khinds10/XBox360Arcade/Construction/21.jpg

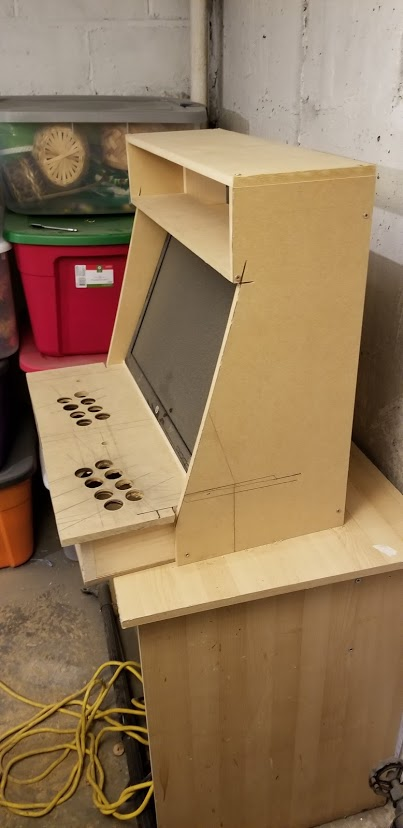
Construction/21.jpg
