khinds10/XBox360Arcade/Construction/24.jpg

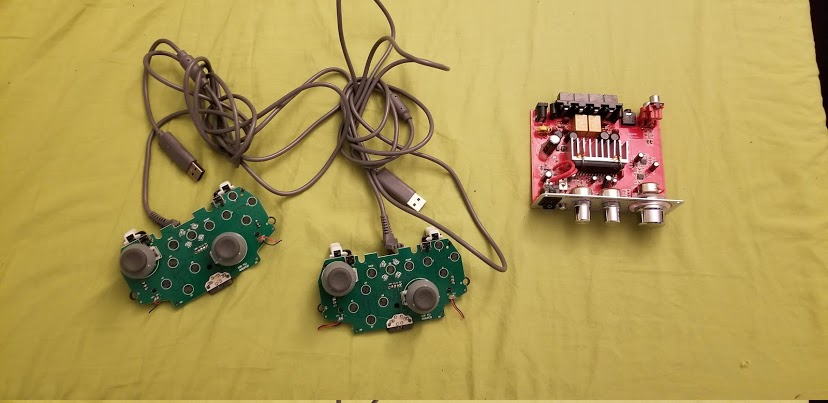
Construction/24.jpg
