khinds10/XBox360Arcade/Construction/25.jpg

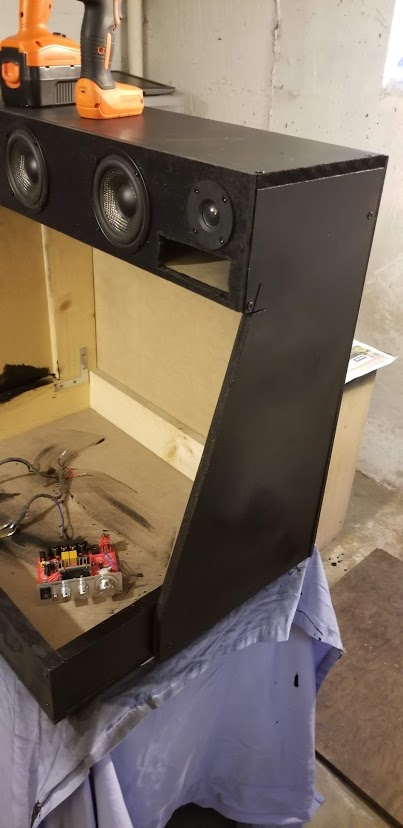
Construction/25.jpg
