khinds10/XBox360Arcade/Construction/29.jpg

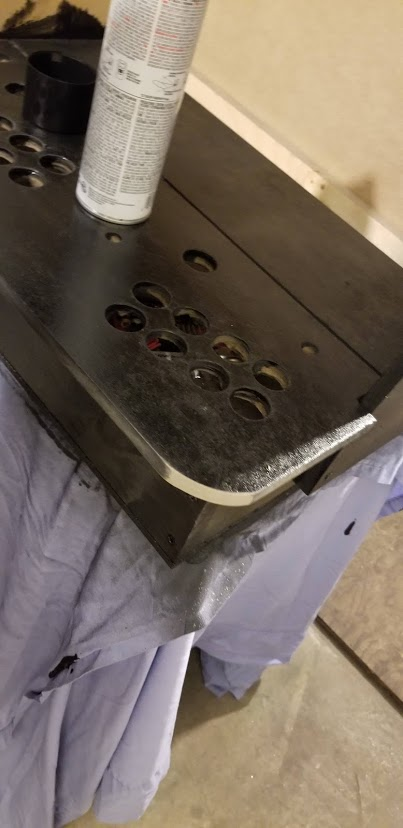
Construction/29.jpg
