khinds10/XBox360Arcade/Construction/35.jpg

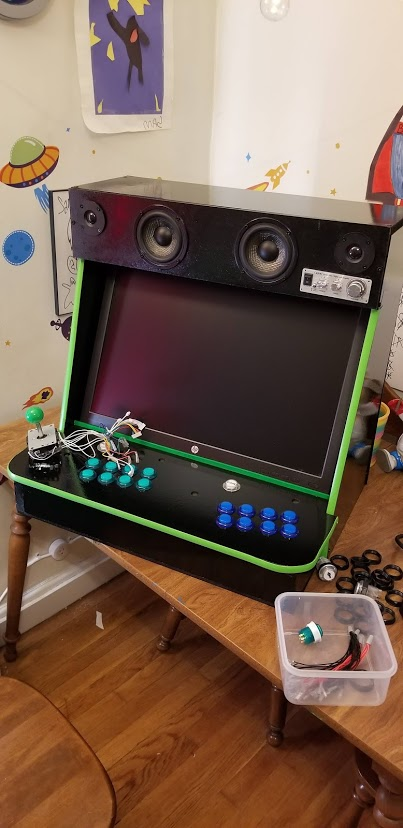
Construction/35.jpg
