khinds10/XBox360Arcade/Construction/36.jpg

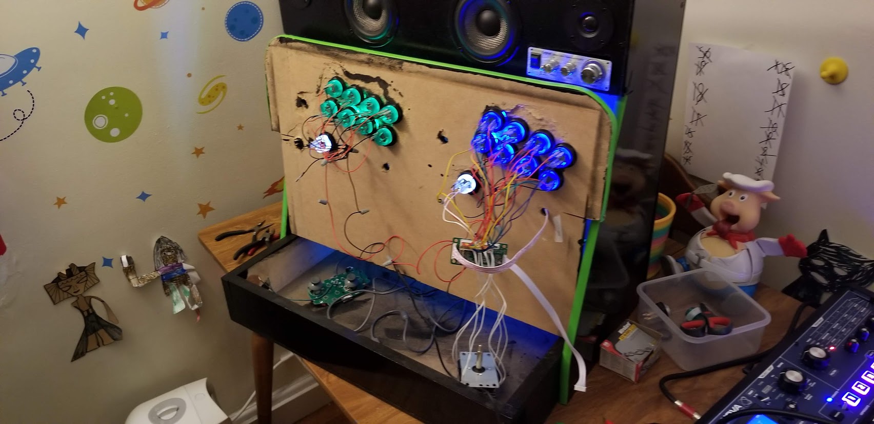
Construction/36.jpg
