khinds10/XBox360Arcade/Construction/40.jpg

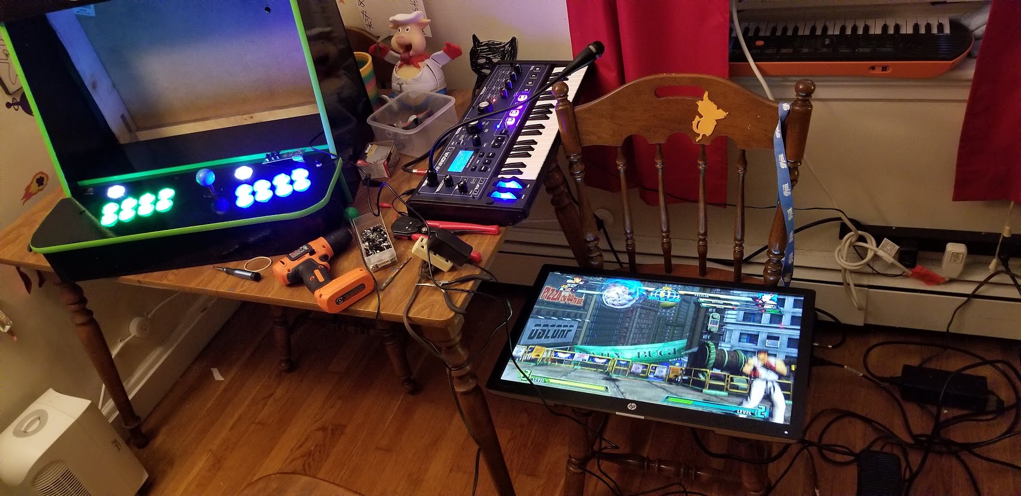
Construction/40.jpg
