khinds10/XBox360Arcade/Construction/42.jpg

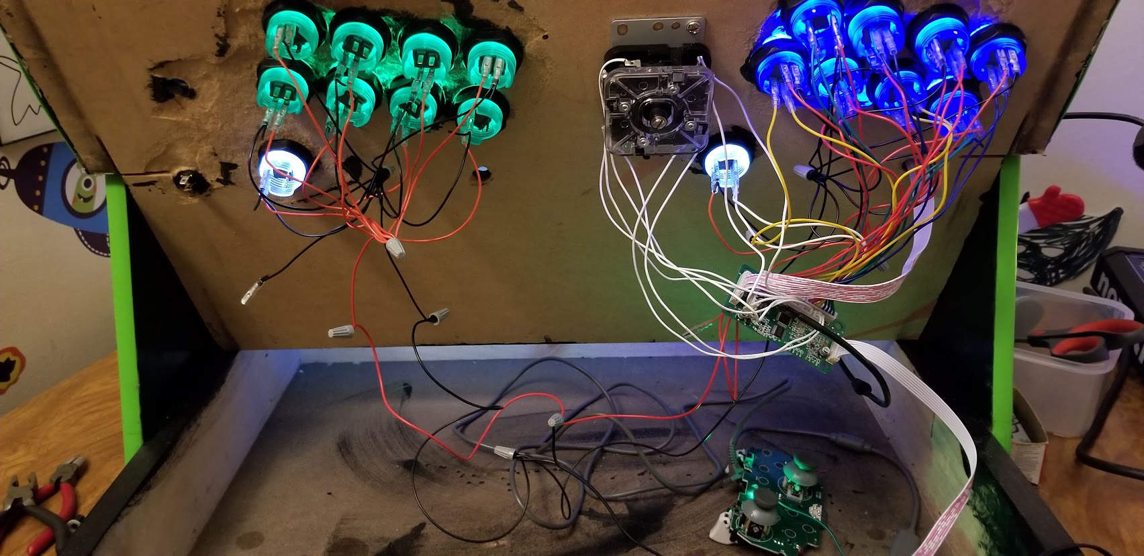
Construction/42.jpg
