khinds10/XBox360Arcade/Construction/47.jpg

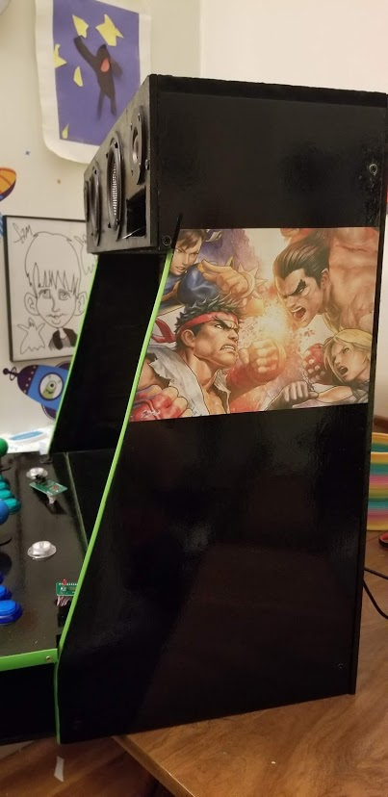
Construction/47.jpg
