khinds10/XBox360Arcade/Construction/53.jpg

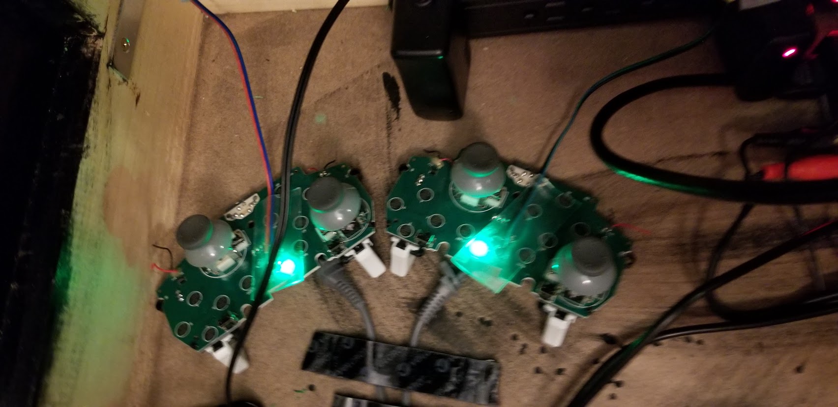
Construction/53.jpg
