khinds10/XBox360Arcade/Construction/54.jpg

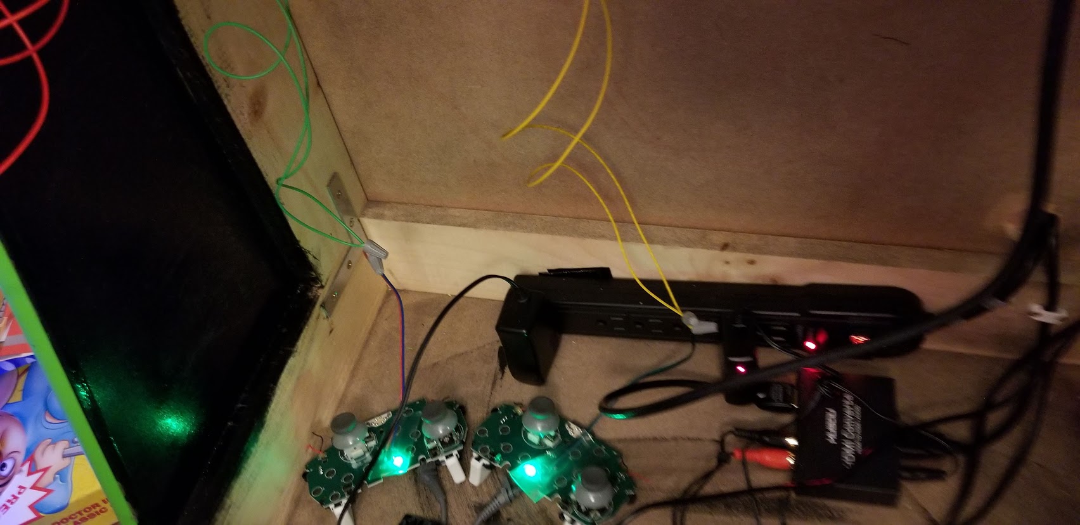
Construction/54.jpg
