khinds10/XBox360Arcade/Construction/69.jpg

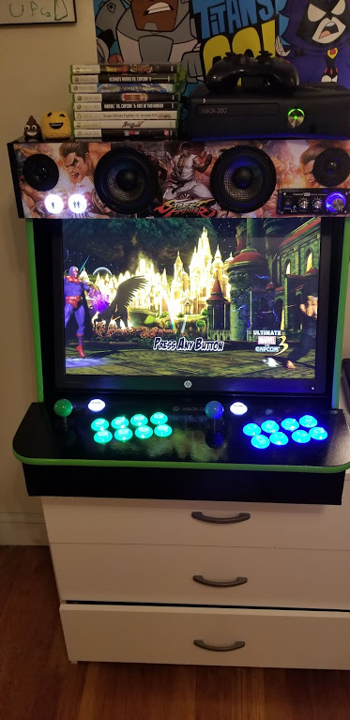
Construction/69.jpg
